keyaki-namiki/universal16/alpha/PCB/universal16.sch

## KiCad design alpha/PCB/universal16.sch (2018-10-19, an earlier design)

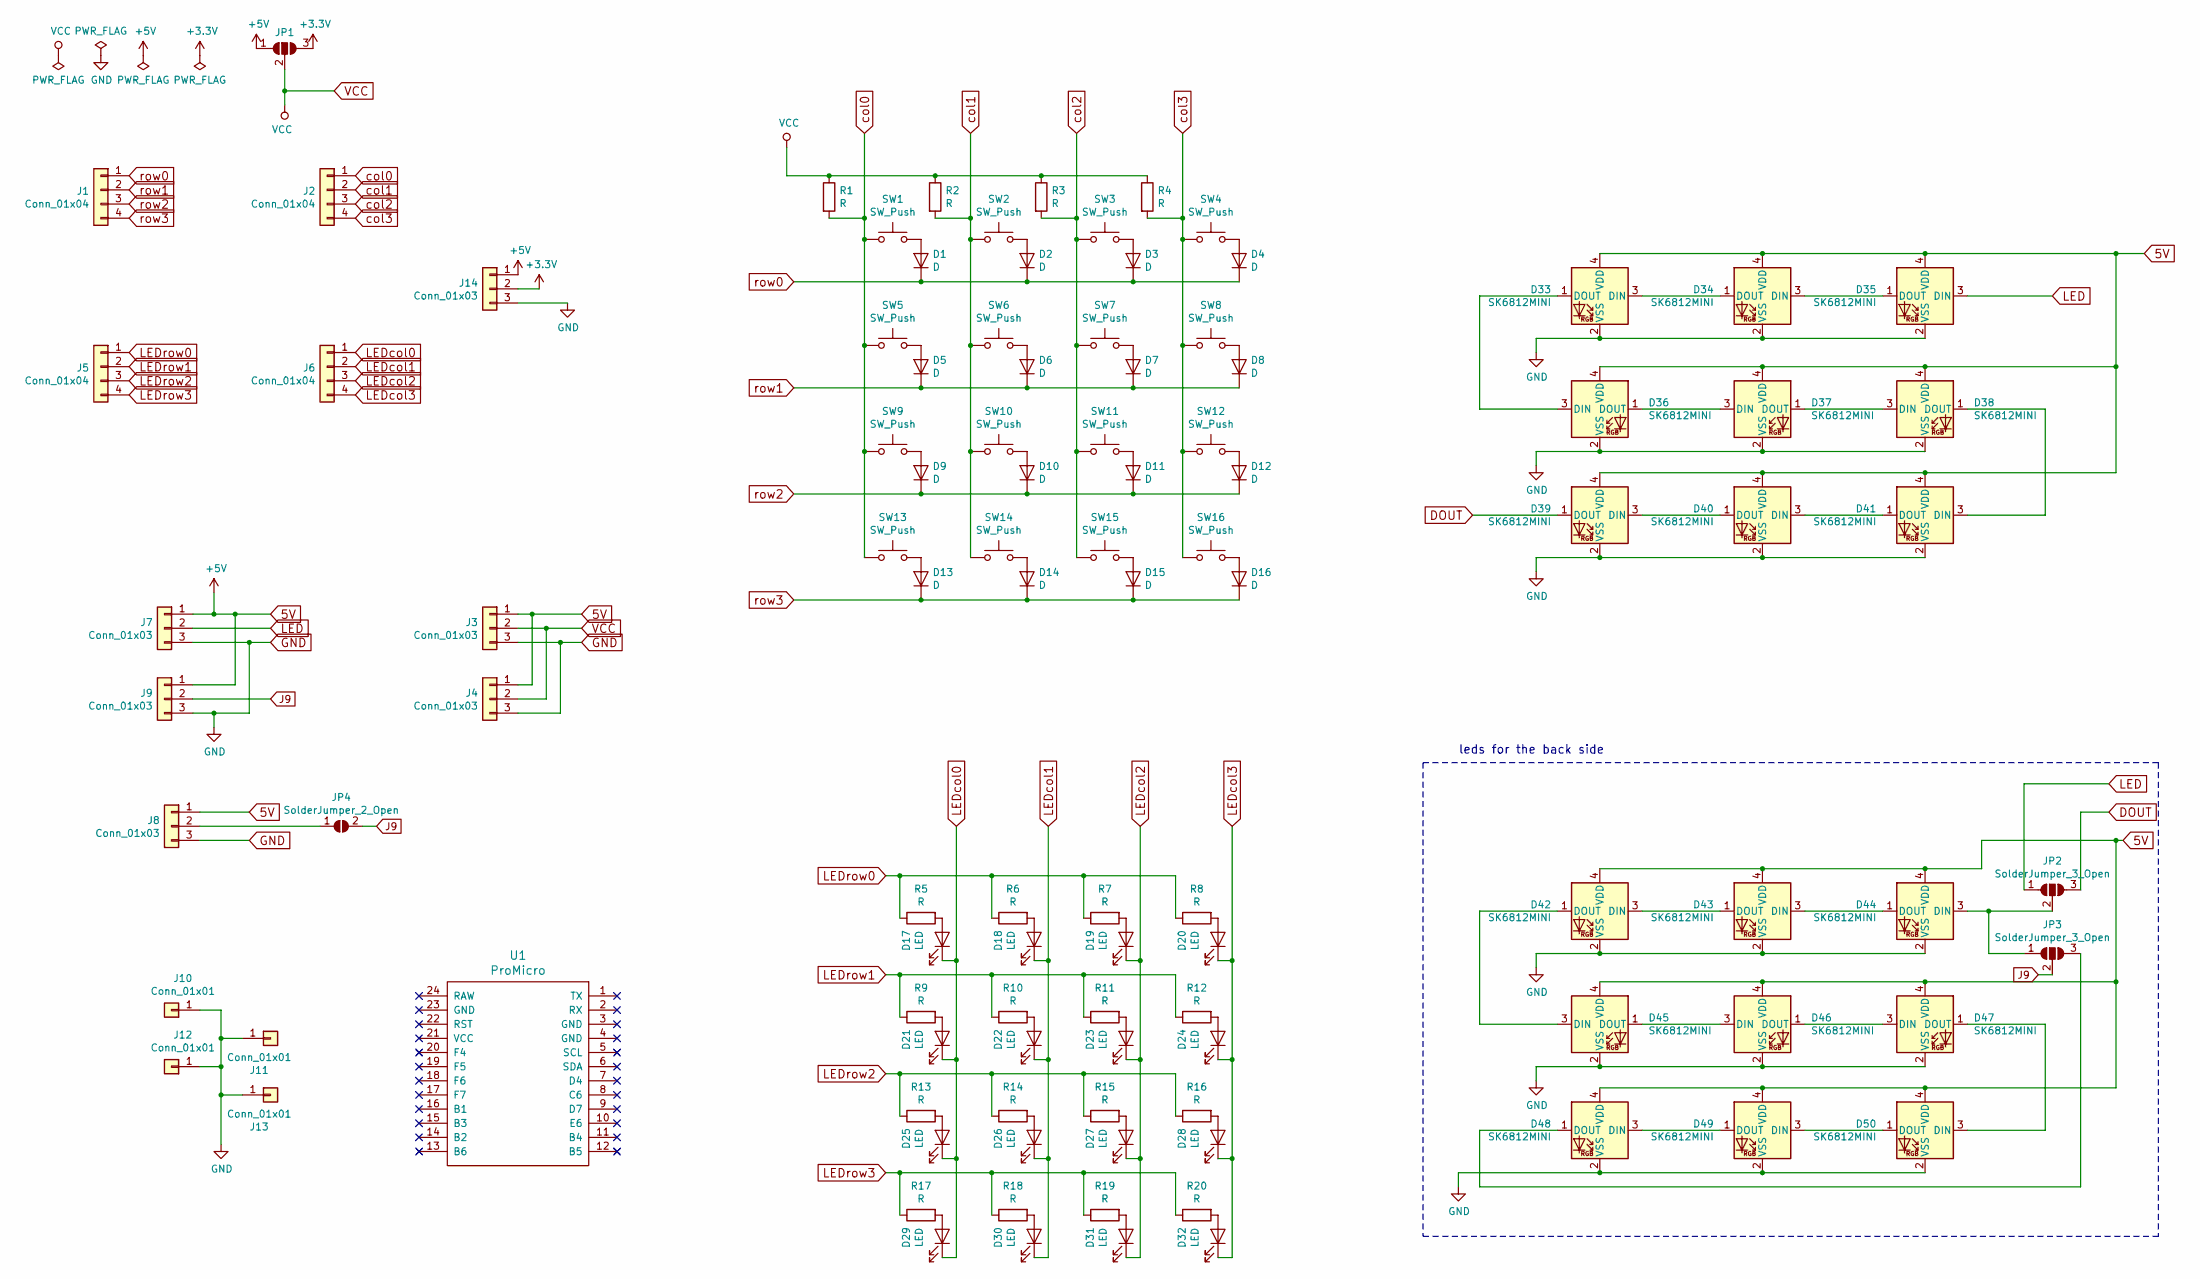
[picture p21: schematic universal16.sch]

Parts:
D1, D2, D3, D4, D5, D6, D7, D8, D9, D10, D11, D12, D13, D14, D15, D16: D; D_SOD123_axial
D17, D18, D19, D20, D21, D22, D23, D24, D25, D26, D27, D28, D29, D30, D31, D32: LED; LED_D3.0mm_Clear
D33, D34, D35, D36, D37, D38, D39, D40, D41, D42, D43, D44, D45, D46, D47, D48, D49, D50: SK6812MINI; LED_SK6812MINI_PLCC4_3.5x3.5mm_P1.75mm
J1, J2, J5, J6: Conn_01x04; PinSocket_1x04_P2.54mm_Vertical
J3, J4, J7, J8, J9, J14: Conn_01x03; PinSocket_1x03_P2.54mm_Vertical
J10, J11, J12, J13: Conn_01x01; MountingHole_2.2mm_M2_Pad_Via
JP1, JP2, JP3: SolderJumper_3_Open; SolderJumper-3_P1.3mm_Open_Pad1.0x1.5mm_NumberLabels
JP4: SolderJumper_2_Open; SolderJumper-2_P1.3mm_Open_Pad1.0x1.5mm
R1, R2, R3, R4, R5, R6, R7, R8, R9, R10, R11, R12, R13, R14, R15, R16, R17, R18, R19, R20: R; R_1206_3216Metric_Pad1.42x1.75mm_HandSolder
SW1, SW2, SW3, SW4, SW5, SW6, SW7, SW8, SW9, SW10, SW11, SW12, SW13, SW14, SW15, SW16: SW_Push; MXOnly-1U_noled
U1: ProMicro

Connections:
+3.3V: J14.2, JP1.3 (B)
+5V: D33.4 (VDD), D34.4 (VDD), D35.4 (VDD), D36.4 (VDD), D37.4 (VDD), D38.4 (VDD), D39.4 (VDD), D40.4 (VDD), D41.4 (VDD), D42.4 (VDD), D43.4 (VDD), D44.4 (VDD), D45.4 (VDD), D46.4 (VDD), D47.4 (VDD), D48.4 (VDD), D49.4 (VDD), D50.4 (VDD), J3.1, J4.1, J7.1, J8.1, J9.1, J14.1, JP1.1 (A)
DOUT: D39.1 (DOUT), JP2.3 (B)
GND: D33.2 (VSS), D34.2 (VSS), D35.2 (VSS), D36.2 (VSS), D37.2 (VSS), D38.2 (VSS), D39.2 (VSS), D40.2 (VSS), D41.2 (VSS), D42.2 (VSS), D43.2 (VSS), D44.2 (VSS), D45.2 (VSS), D46.2 (VSS), D47.2 (VSS), D48.2 (VSS), D49.2 (VSS), D50.2 (VSS), J3.3, J4.3, J7.3, J8.3, J9.3, J10.1, J11.1, J12.1, J13.1, J14.3
J9: J9.2, JP3.2 (C), JP4.2 (B)
LED: D35.3 (DIN), J7.2, JP2.1 (A)
LEDcol0: D17.1 (K), D21.1 (K), D25.1 (K), D29.1 (K), J6.1
LEDcol1: D18.1 (K), D22.1 (K), D26.1 (K), D30.1 (K), J6.2
LEDcol2: D19.1 (K), D23.1 (K), D27.1 (K), D31.1 (K), J6.3
LEDcol3: D20.1 (K), D24.1 (K), D28.1 (K), D32.1 (K), J6.4
LEDrow0: J5.1, R5.1, R6.1, R7.1, R8.1
LEDrow1: J5.2, R9.1, R10.1, R11.1, R12.1
LEDrow2: J5.3, R13.1, R14.1, R15.1, R16.1
LEDrow3: J5.4, R17.1, R18.1, R19.1, R20.1
unnamed: D1.2 (A), SW1.2
unnamed: D2.2 (A), SW2.2
unnamed: D3.2 (A), SW3.2
unnamed: D4.2 (A), SW4.2
unnamed: D5.2 (A), SW5.2
unnamed: D6.2 (A), SW6.2
unnamed: D7.2 (A), SW7.2
unnamed: D8.2 (A), SW8.2
unnamed: D9.2 (A), SW9.2
unnamed: D10.2 (A), SW10.2
unnamed: D11.2 (A), SW11.2
unnamed: D12.2 (A), SW12.2
unnamed: D13.2 (A), SW13.2
unnamed: D14.2 (A), SW14.2
unnamed: D15.2 (A), SW15.2
unnamed: D16.2 (A), SW16.2
unnamed: D17.2 (A), R5.2
unnamed: D18.2 (A), R6.2
unnamed: D19.2 (A), R7.2
unnamed: D20.2 (A), R8.2
unnamed: D21.2 (A), R9.2
unnamed: D22.2 (A), R10.2
unnamed: D23.2 (A), R11.2
unnamed: D24.2 (A), R12.2
unnamed: D25.2 (A), R13.2
unnamed: D26.2 (A), R14.2
unnamed: D27.2 (A), R15.2
unnamed: D28.2 (A), R16.2
unnamed: D29.2 (A), R17.2
unnamed: D30.2 (A), R18.2
unnamed: D31.2 (A), R19.2
unnamed: D32.2 (A), R20.2
unnamed: D33.1 (DOUT), D36.3 (DIN)
unnamed: D33.3 (DIN), D34.1 (DOUT)
unnamed: D34.3 (DIN), D35.1 (DOUT)
unnamed: D36.1 (DOUT), D37.3 (DIN)
unnamed: D37.1 (DOUT), D38.3 (DIN)
unnamed: D38.1 (DOUT), D41.3 (DIN)
unnamed: D39.3 (DIN), D40.1 (DOUT)
unnamed: D40.3 (DIN), D41.1 (DOUT)
unnamed: D42.1 (DOUT), D45.3 (DIN)
unnamed: D42.3 (DIN), D43.1 (DOUT)
unnamed: D43.3 (DIN), D44.1 (DOUT)
unnamed: D44.3 (DIN), JP2.2 (C), JP3.1 (A)
unnamed: D45.1 (DOUT), D46.3 (DIN)
unnamed: D46.1 (DOUT), D47.3 (DIN)
unnamed: D47.1 (DOUT), D50.3 (DIN)
unnamed: D48.1 (DOUT), JP3.3 (B)
unnamed: D48.3 (DIN), D49.1 (DOUT)
unnamed: D49.3 (DIN), D50.1 (DOUT)
unnamed: J8.2, JP4.1 (A)
VCC: J3.2, J4.2, JP1.2 (C), R1.1, R2.1, R3.1, R4.1
col0: J2.1, R1.2, SW1.1, SW5.1, SW9.1, SW13.1
col1: J2.2, R2.2, SW2.1, SW6.1, SW10.1, SW14.1
col2: J2.3, R3.2, SW3.1, SW7.1, SW11.1, SW15.1
col3: J2.4, R4.2, SW4.1, SW8.1, SW12.1, SW16.1
row0: D1.1 (K), D2.1 (K), D3.1 (K), D4.1 (K), J1.1
row1: D5.1 (K), D6.1 (K), D7.1 (K), D8.1 (K), J1.2
row2: D9.1 (K), D10.1 (K), D11.1 (K), D12.1 (K), J1.3
row3: D13.1 (K), D14.1 (K), D15.1 (K), D16.1 (K), J1.4

Notes on the sheet:
leds for the back side
