keyaki-namiki/universal16/case/PCB/p4vert_v03/p4vert_bottom.sch

## KiCad design case/PCB/p4vert_v03/p4vert_bottom.sch (2019-03-03)

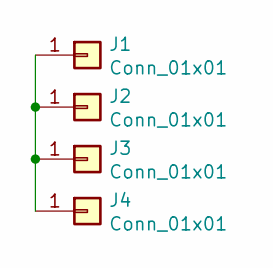
[picture p22: schematic p4vert_bottom.sch]

Parts:
J1, J2, J3, J4: Conn_01x01; MountingHole_2.2mm_M2_Pad

Connections:
unnamed: J1.1, J2.1, J3.1, J4.1
