keyaki-namiki/universal16/p4vert/PCB/v0.3c/p4vert.sch

## KiCad design p4vert/PCB/v0.3c/p4vert.sch (2019-03-03, an earlier design)

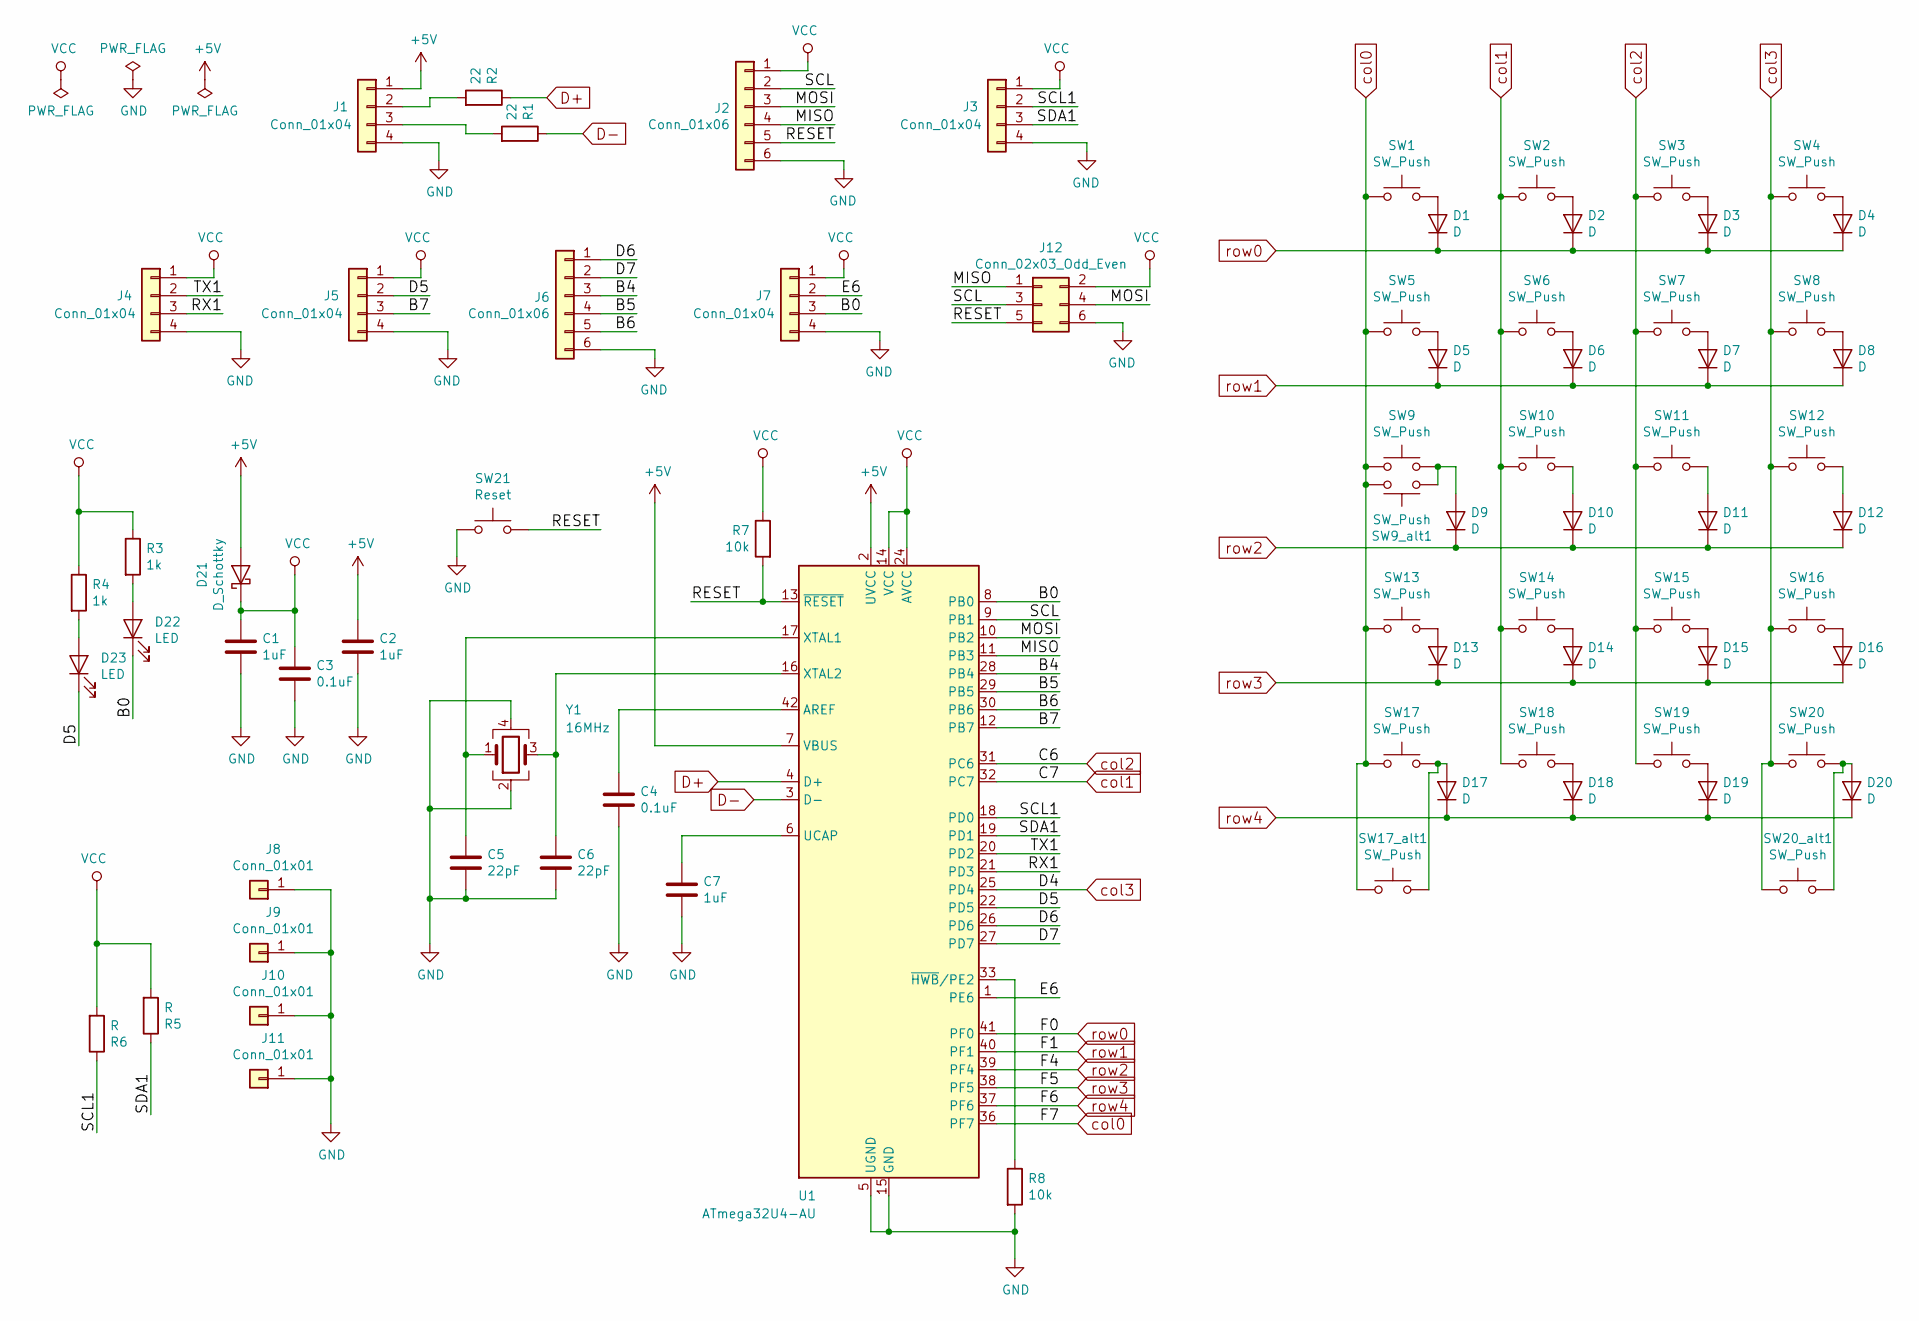
[picture p23: schematic p4vert.sch]

Parts:
C1, C2, C7: 1uF; C_0603_1608Metric_Pad1.05x0.95mm_HandSolder
C3, C4: 0.1uF; C_0603_1608Metric_Pad1.05x0.95mm_HandSolder
C5, C6: 22pF; C_0603_1608Metric_Pad1.05x0.95mm_HandSolder
D1, D2, D3, D4, D5, D6, D7, D8, D9, D10, D11, D12, D13, D14, D15, D16, D17, D18, D19, D20: D; D_SOD-123
D21: D_Schottky; D_SOD-123
D22, D23: LED; LED_0603_1608Metric_Pad1.05x0.95mm_HandSolder
J1: Conn_01x04; 4pads_large
J2, J6: Conn_01x06; 6pads
J3, J4, J5, J7: Conn_01x04; 4pads
J8, J9, J10, J11: Conn_01x01; TestPoint_Plated_Hole_D5.0mm
J12: Conn_02x03_Odd_Even; PinHeader_2x03_P2.54mm_Vertical
R1, R2: 22; R_0603_1608Metric_Pad1.05x0.95mm_HandSolder
R3, R4: 1k; R_0603_1608Metric_Pad1.05x0.95mm_HandSolder
R5, R6: R; R_0603_1608Metric_Pad1.05x0.95mm_HandSolder
R7, R8: 10k; R_0603_1608Metric_Pad1.05x0.95mm_HandSolder
SW1, SW2, SW3, SW4, SW5, SW6, SW7, SW8, SW9, SW10, SW11, SW12, SW13, SW14, SW15, SW16, SW17, SW18, SW19, SW20: SW_Push; MXOnly-1U_noled
SW9_alt1, SW17_alt1, SW20_alt1: SW_Push; MXOnly-2U-noled
SW21: Reset; SW_ALPS_SKRP
U1: ATmega32U4-AU; TQFP-44_10x10mm_P0.8mm
Y1: 16MHz; Crystal_SMD_3225-4Pin_3.2x2.5mm_HandSoldering

Connections:
+5V: C2.1, D21.2 (A), J1.1, U1.2 (UVCC), U1.7 (VBUS)
B0: D22.1 (K), J7.3, U1.8 (PB0)
B4: J6.3, U1.28 (PB4)
B5: J6.4, U1.29 (PB5)
B6: J6.5, U1.30 (PB6)
B7: J5.3, U1.12 (PB7)
D5: D23.1 (K), J5.2, U1.22 (PD5)
D6: J6.1, U1.26 (PD6)
D7: J6.2, U1.27 (PD7)
D+: R2.1, U1.4 (D+)
D-: R1.1, U1.3 (D-)
E6: J7.2, U1.1 (PE6)
GND: C1.2, C2.2, C3.2, C4.2, C5.2, C6.2, C7.2, J1.4, J2.6, J3.4, J4.4, J5.4, J6.6, J7.4, J8.1, J9.1, J10.1, J11.1, J12.6, R8.2, SW21.1, U1.5 (UGND), U1.15 (GND), U1.23 (GND), U1.35 (GND), U1.43 (GND), Y1.2, Y1.4
MISO: J2.4, J12.1, U1.11 (PB3)
MOSI: J2.3, J12.4, U1.10 (PB2)
unnamed: C4.1, U1.42 (AREF)
unnamed: C5.1, U1.17 (XTAL1), Y1.1
unnamed: C6.1, U1.16 (XTAL2), Y1.3
unnamed: C7.1, U1.6 (UCAP)
unnamed: D1.2 (A), SW1.2
unnamed: D2.2 (A), SW2.2
unnamed: D3.2 (A), SW3.2
unnamed: D4.2 (A), SW4.2
unnamed: D5.2 (A), SW5.2
unnamed: D6.2 (A), SW6.2
unnamed: D7.2 (A), SW7.2
unnamed: D8.2 (A), SW8.2
unnamed: D9.2 (A), SW9.2, SW9_alt1.2
unnamed: D10.2 (A), SW10.2
unnamed: D11.2 (A), SW11.2
unnamed: D12.2 (A), SW12.2
unnamed: D13.2 (A), SW13.2
unnamed: D14.2 (A), SW14.2
unnamed: D15.2 (A), SW15.2
unnamed: D16.2 (A), SW16.2
unnamed: D17.2 (A), SW17.2, SW17_alt1.2
unnamed: D18.2 (A), SW18.2
unnamed: D19.2 (A), SW19.2
unnamed: D20.2 (A), SW20.2, SW20_alt1.2
unnamed: D22.2 (A), R3.2
unnamed: D23.2 (A), R4.2
unnamed: J1.2, R2.2
unnamed: J1.3, R1.2
unnamed: R8.1, U1.33 (~HWB~/PE2)
RESET: J2.5, J12.5, R7.2, SW21.2, U1.13 (~RESET)
RX1: J4.3, U1.21 (PD3)
SCL: J2.2, J12.3, U1.9 (PB1)
SCL1: J3.2, R6.1, U1.18 (PD0)
SDA1: J3.3, R5.1, U1.19 (PD1)
TX1: J4.2, U1.20 (PD2)
VCC: C1.1, C3.1, D21.1 (K), J2.1, J3.1, J4.1, J5.1, J7.1, J12.2, R3.1, R4.1, R5.2, R6.2, R7.1, U1.14 (VCC), U1.24 (AVCC), U1.34 (VCC), U1.44 (AVCC)
col0: SW1.1, SW5.1, SW9.1, SW9_alt1.1, SW13.1, SW17.1, SW17_alt1.1, U1.36 (PF7)
col1: SW2.1, SW6.1, SW10.1, SW14.1, SW18.1, U1.32 (PC7)
col2: SW3.1, SW7.1, SW11.1, SW15.1, SW19.1, U1.31 (PC6)
col3: SW4.1, SW8.1, SW12.1, SW16.1, SW20.1, SW20_alt1.1, U1.25 (PD4)
row0: D1.1 (K), D2.1 (K), D3.1 (K), D4.1 (K), U1.41 (PF0)
row1: D5.1 (K), D6.1 (K), D7.1 (K), D8.1 (K), U1.40 (PF1)
row2: D9.1 (K), D10.1 (K), D11.1 (K), D12.1 (K), U1.39 (PF4)
row3: D13.1 (K), D14.1 (K), D15.1 (K), D16.1 (K), U1.38 (PF5)
row4: D17.1 (K), D18.1 (K), D19.1 (K), D20.1 (K), U1.37 (PF6)
