keyaki-namiki/universal16/plus4/PCB/v0.2/universal16p4.sch

## KiCad design plus4/PCB/v0.2/universal16p4.sch (2018-10-27)

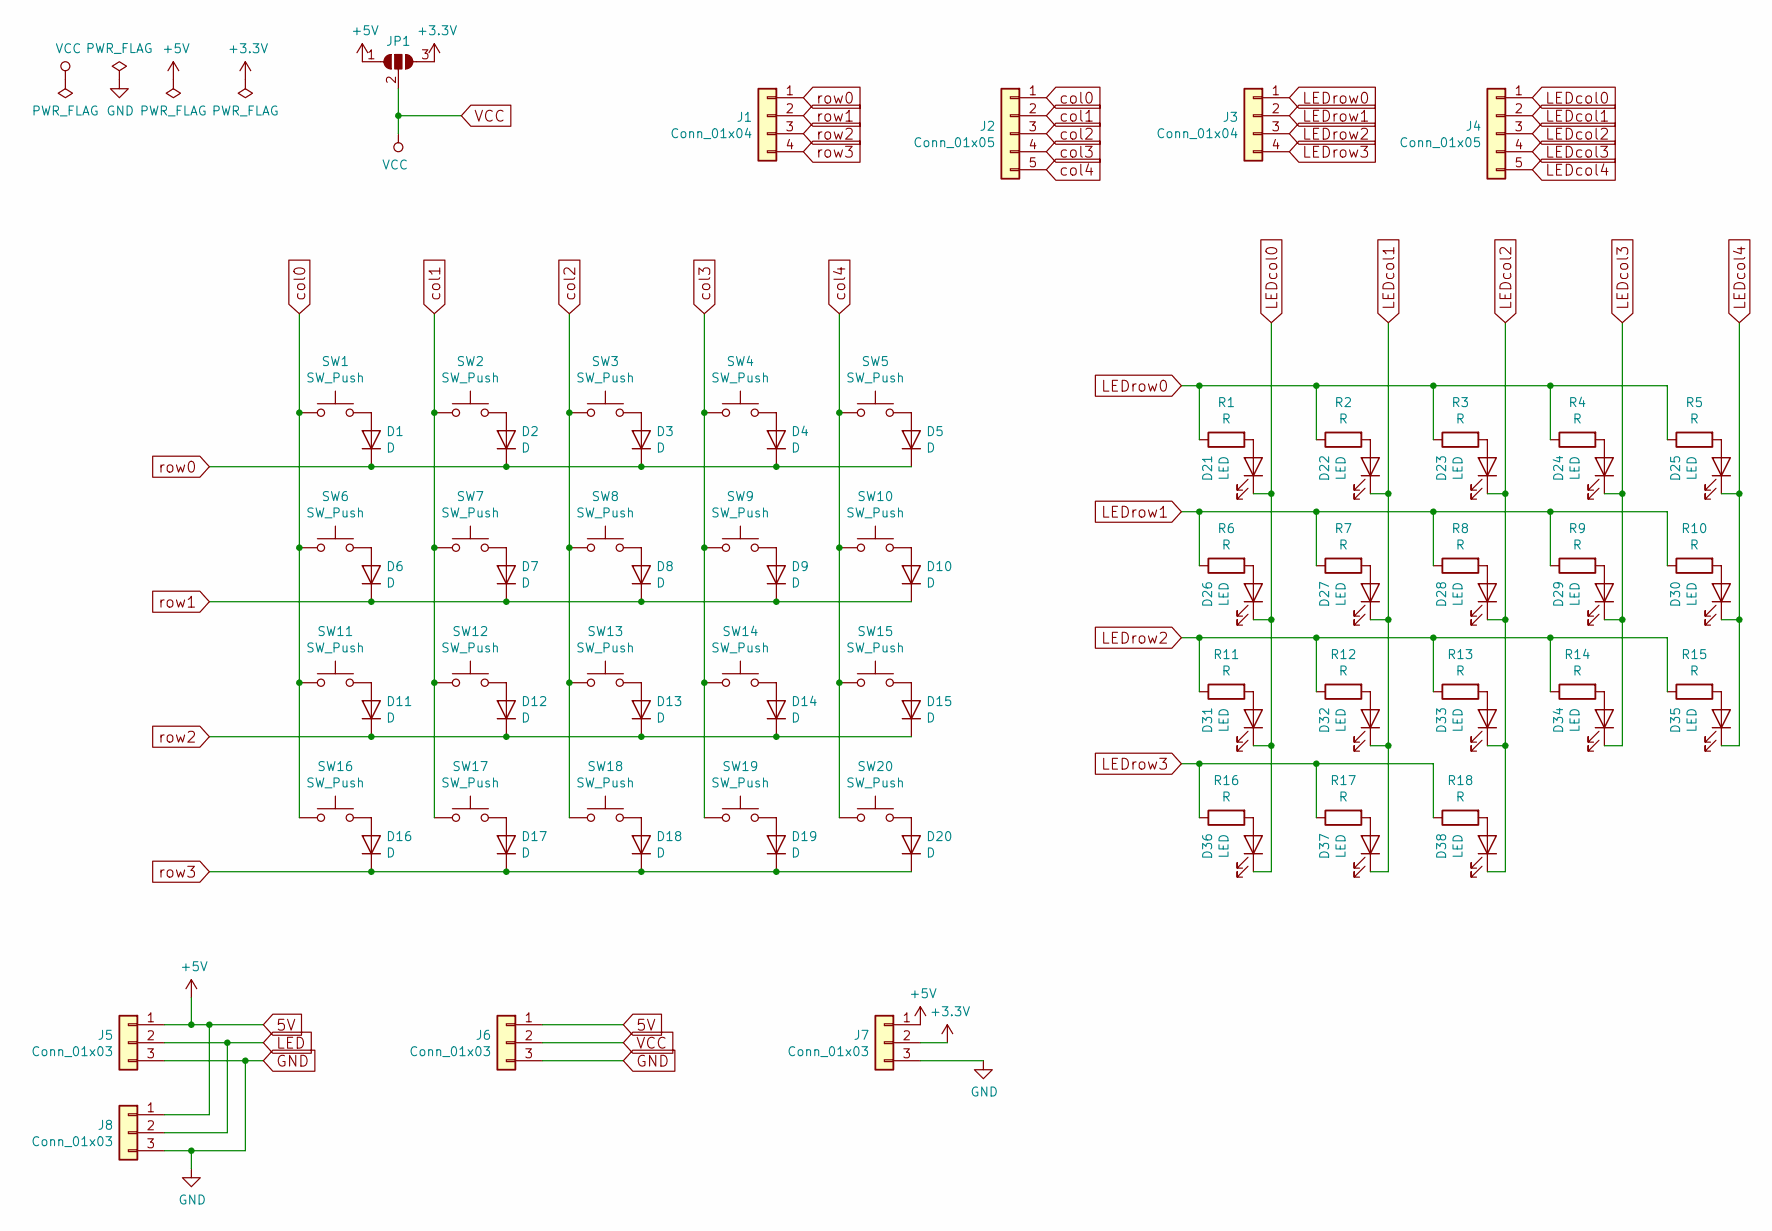
[picture p24: schematic universal16p4.sch]

Parts:
D1, D2, D3, D4, D5, D6, D7, D8, D9, D10, D11, D12, D13, D14, D15, D16, D17, D18, D19, D20: D; D_SOD123_axial
D21, D22, D23, D24, D25, D26, D27, D28, D29, D30, D31, D32, D33, D34, D35, D36, D37, D38: LED; LED_D3.0mm_Clear
J1, J3: Conn_01x04; 4pads
J2, J4: Conn_01x05; 5pads
J5, J6, J7, J8: Conn_01x03; 3pads
JP1: SolderJumper_3_Open; SolderJumper-3_P1.3mm_Open_Pad1.0x1.5mm_NumberLabels
R1, R2, R3, R4, R5, R6, R7, R8, R9, R10, R11, R12, R13, R14, R15, R16, R17, R18: R; R_1206_3216Metric_Pad1.42x1.75mm_HandSolder
SW1, SW2, SW3, SW4, SW5, SW6, SW7, SW8, SW9, SW10, SW11, SW12, SW13, SW14, SW15, SW16, SW17, SW18, SW19, SW20: SW_Push; MXonly-1U-flip-kailh_lp

Connections:
+3.3V: J7.2, JP1.3 (B)
+5V: J5.1, J6.1, J7.1, J8.1, JP1.1 (A)
GND: J5.3, J6.3, J7.3, J8.3
LED: J5.2, J8.2
LEDcol0: D21.1 (K), D26.1 (K), D31.1 (K), D36.1 (K), J4.1
LEDcol1: D22.1 (K), D27.1 (K), D32.1 (K), D37.1 (K), J4.2
LEDcol2: D23.1 (K), D28.1 (K), D33.1 (K), D38.1 (K), J4.3
LEDcol3: D24.1 (K), D29.1 (K), D34.1 (K), J4.4
LEDcol4: D25.1 (K), D30.1 (K), D35.1 (K), J4.5
LEDrow0: J3.1, R1.1, R2.1, R3.1, R4.1, R5.1
LEDrow1: J3.2, R6.1, R7.1, R8.1, R9.1, R10.1
LEDrow2: J3.3, R11.1, R12.1, R13.1, R14.1, R15.1
LEDrow3: J3.4, R16.1, R17.1, R18.1
unnamed: D1.2 (A), SW1.2
unnamed: D2.2 (A), SW2.2
unnamed: D3.2 (A), SW3.2
unnamed: D4.2 (A), SW4.2
unnamed: D5.2 (A), SW5.2
unnamed: D6.2 (A), SW6.2
unnamed: D7.2 (A), SW7.2
unnamed: D8.2 (A), SW8.2
unnamed: D9.2 (A), SW9.2
unnamed: D10.2 (A), SW10.2
unnamed: D11.2 (A), SW11.2
unnamed: D12.2 (A), SW12.2
unnamed: D13.2 (A), SW13.2
unnamed: D14.2 (A), SW14.2
unnamed: D15.2 (A), SW15.2
unnamed: D16.2 (A), SW16.2
unnamed: D17.2 (A), SW17.2
unnamed: D18.2 (A), SW18.2
unnamed: D19.2 (A), SW19.2
unnamed: D20.2 (A), SW20.2
unnamed: D21.2 (A), R1.2
unnamed: D22.2 (A), R2.2
unnamed: D23.2 (A), R3.2
unnamed: D24.2 (A), R4.2
unnamed: D25.2 (A), R5.2
unnamed: D26.2 (A), R6.2
unnamed: D27.2 (A), R7.2
unnamed: D28.2 (A), R8.2
unnamed: D29.2 (A), R9.2
unnamed: D30.2 (A), R10.2
unnamed: D31.2 (A), R11.2
unnamed: D32.2 (A), R12.2
unnamed: D33.2 (A), R13.2
unnamed: D34.2 (A), R14.2
unnamed: D35.2 (A), R15.2
unnamed: D36.2 (A), R16.2
unnamed: D37.2 (A), R17.2
unnamed: D38.2 (A), R18.2
VCC: J6.2, JP1.2 (C)
col0: J2.1, SW1.1, SW6.1, SW11.1, SW16.1
col1: J2.2, SW2.1, SW7.1, SW12.1, SW17.1
col2: J2.3, SW3.1, SW8.1, SW13.1, SW18.1
col3: J2.4, SW4.1, SW9.1, SW14.1, SW19.1
col4: J2.5, SW5.1, SW10.1, SW15.1, SW20.1
row0: D1.1 (K), D2.1 (K), D3.1 (K), D4.1 (K), D5.1 (K), J1.1
row1: D6.1 (K), D7.1 (K), D8.1 (K), D9.1 (K), D10.1 (K), J1.2
row2: D11.1 (K), D12.1 (K), D13.1 (K), D14.1 (K), D15.1 (K), J1.3
row3: D16.1 (K), D17.1 (K), D18.1 (K), D19.1 (K), D20.1 (K), J1.4
